kreddy-nelakurti/UniQHW/Components/KP15B-6S-SF_800_/KP15B-6S-SF_800_.step

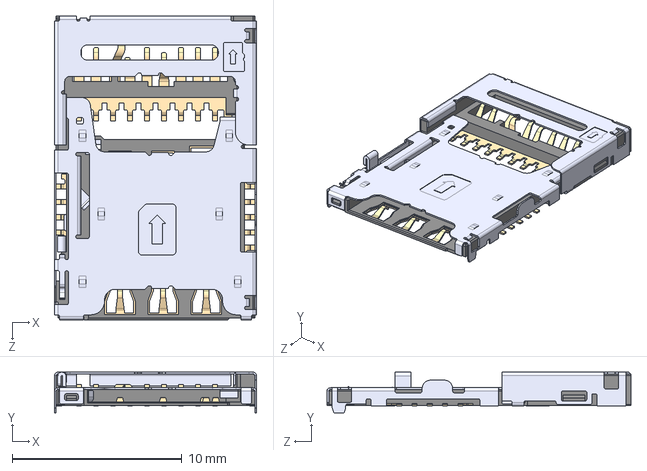
[picture p15: CAD file, 2026-02-27]
Components/KP15B-6S-SF_800_/KP15B-6S-SF_800_.step
11.9 x 2.40 x 17.9 mm
