kreddy-nelakurti/UniQHW/Components/LightOn-LEDs/LTST-C193KRKT-5A.step

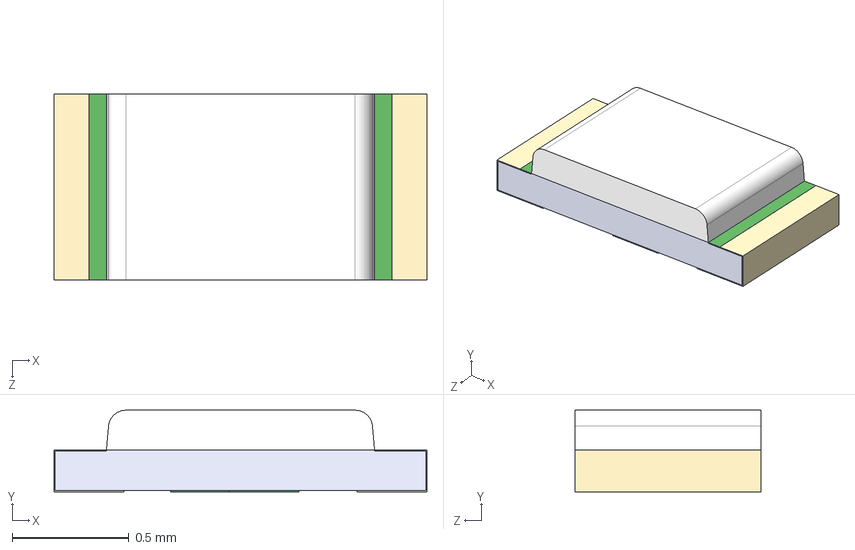
[picture p16: CAD file, 2026-02-27]
Components/LightOn-LEDs/LTST-C193KRKT-5A.step
1.60 x 0.35 x 0.8 mm
