kreddy-nelakurti/UniQHW/Components/MMBT3904LP-7/MMBT3904LP-7.step

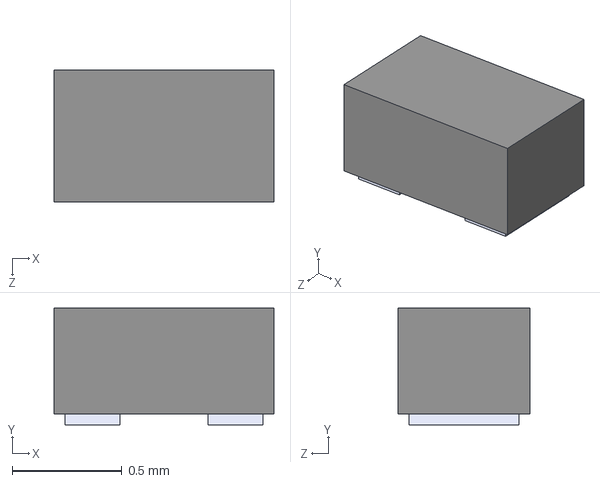
[picture p17: CAD file, 2026-02-27]
Components/MMBT3904LP-7/MMBT3904LP-7.step
1.00 x 0.53 x 0.6 mm
