kreddy-nelakurti/UniQHW/Components/MMBT3904LT1G/MMBT3904LT1G.step

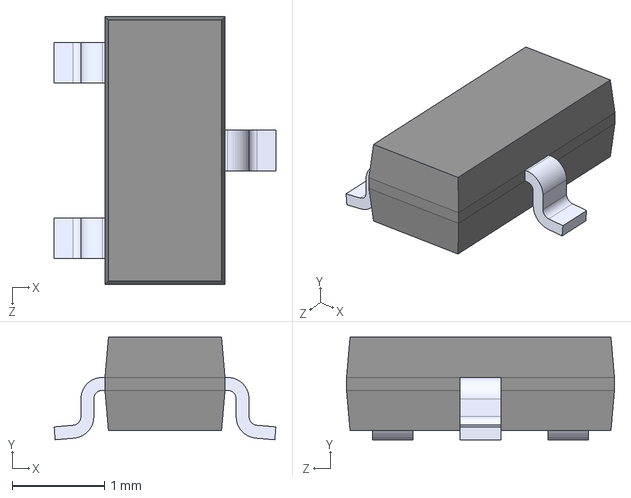
[picture p18: CAD file, 2026-02-27]
Components/MMBT3904LT1G/MMBT3904LT1G.step
2.40 x 1.11 x 2.90 mm
