kreddy-nelakurti/UniQHW/Components/MMSZ5231BT1G/SOD-123_ONS.step

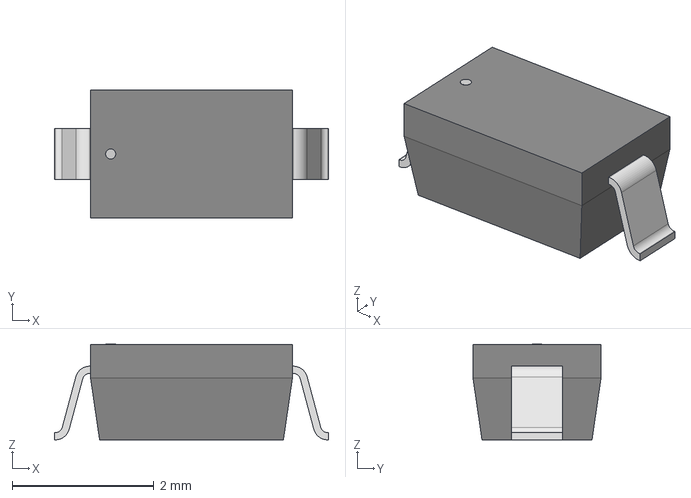
[picture p19: CAD file, 2026-02-27]
Components/MMSZ5231BT1G/SOD-123_ONS.step
3.86 x 1.80 x 1.35 mm
