kreddy-nelakurti/UniQHW/Components/MPZ2012S221AT000/MPZ2012S221AT000.step

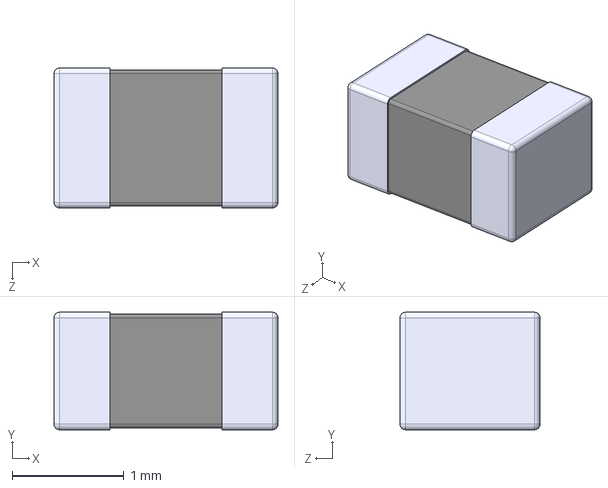
[picture p20: CAD file, 2026-02-27]
Components/MPZ2012S221AT000/MPZ2012S221AT000.step
2.00 x 1.05 x 1.25 mm
