kreddy-nelakurti/UniQHW/Components/PCA9306DQER/PCA9306DQER.step

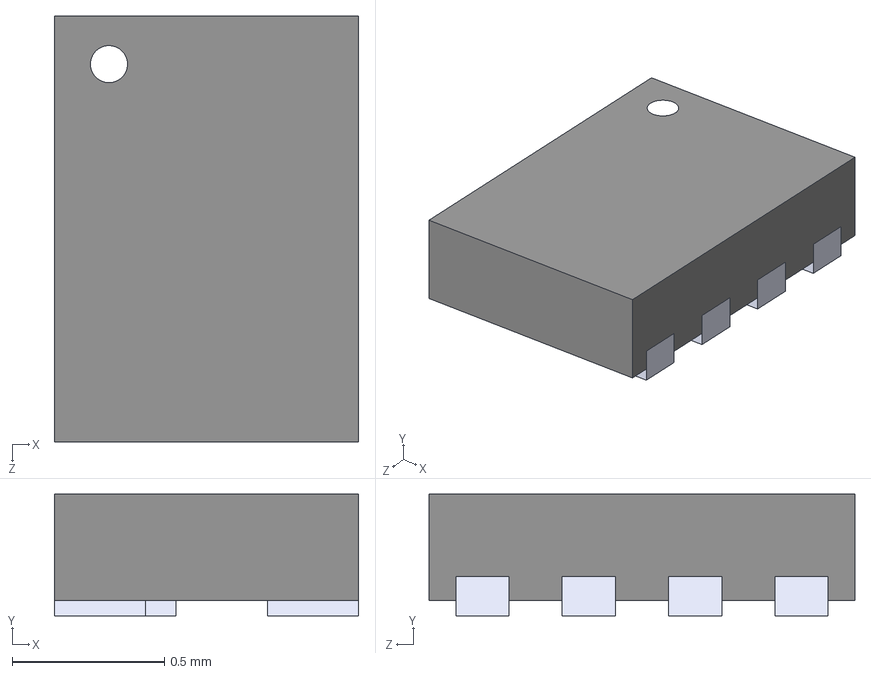
[picture p21: CAD file, 2026-02-27]
Components/PCA9306DQER/PCA9306DQER.step
1.00 x 0.4 x 1.40 mm
