kreddy-nelakurti/UniQHW/Components/S3B-PH-SM4-TB_LF__SN_/S3B-PH-SM4-TB_LF__SN_.step

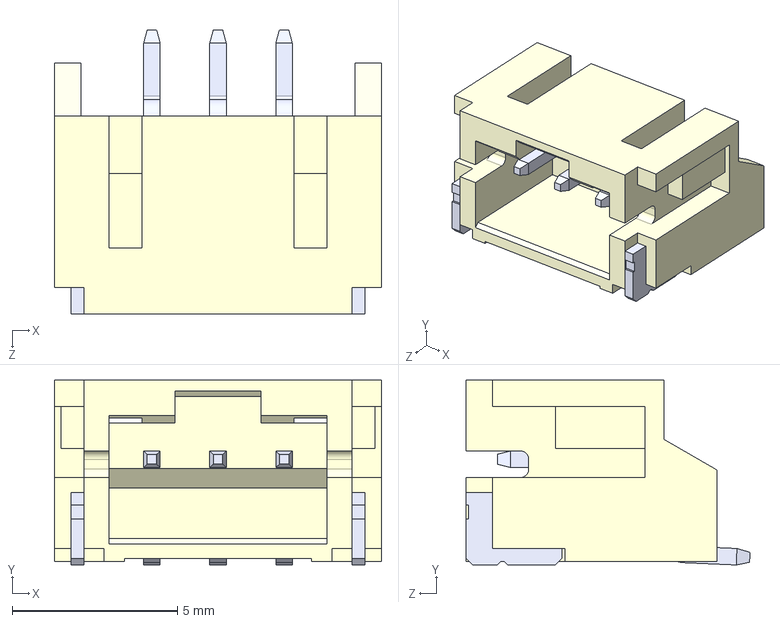
[picture p22: CAD file, 2026-02-27]
Components/S3B-PH-SM4-TB_LF__SN_/S3B-PH-SM4-TB_LF__SN_.step
9.90 x 5.60 x 8.60 mm
