kreddy-nelakurti/UniQHW/Components/SJ-3551B-MSMT-TR-67/SJ-3551B-MSMT-TR-67.step

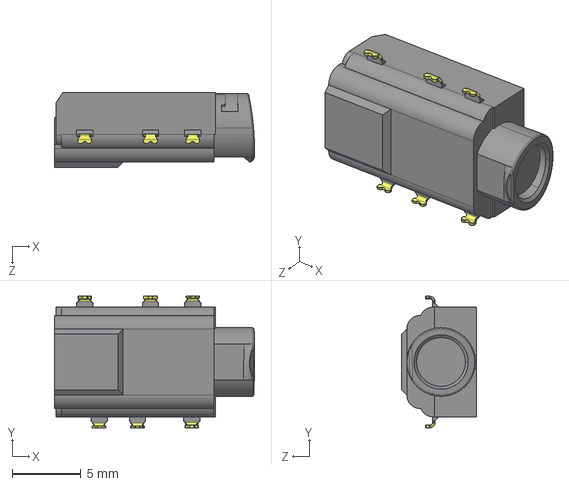
[picture p23: CAD file, 2026-02-27]
Components/SJ-3551B-MSMT-TR-67/SJ-3551B-MSMT-TR-67.step
14.6 x 9.60 x 5.45 mm
