kreddy-nelakurti/UniQHW/Components/SJ-43504-SMT-TR/SJ-43504-SMT-TR.step

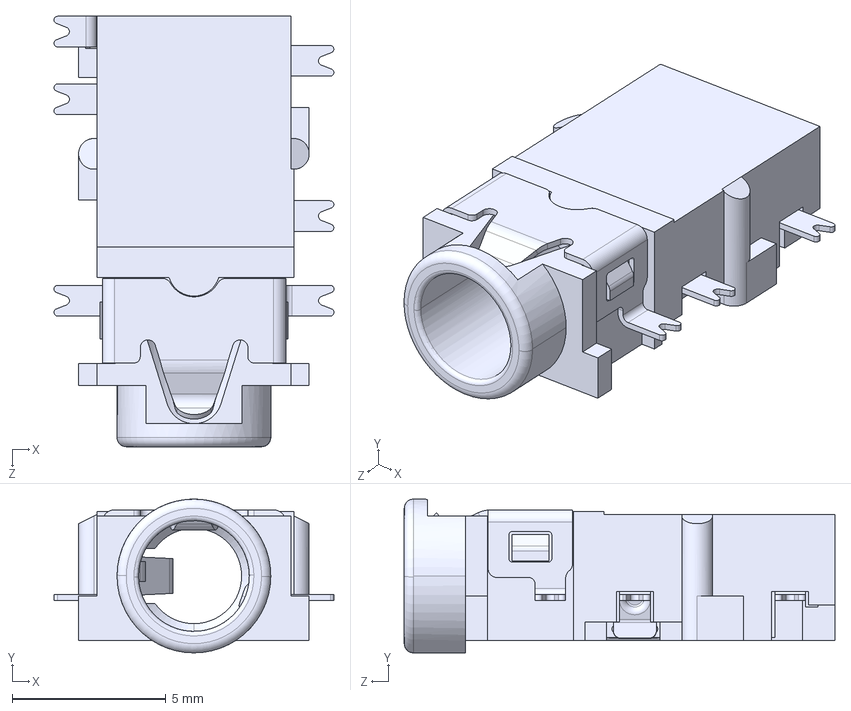
[picture p24: CAD file, 2026-02-27]
Components/SJ-43504-SMT-TR/SJ-43504-SMT-TR.step
9.10 x 5.00 x 14.0 mm
