kreddy-nelakurti/UniQHW/Components/SJ-43515RS-SMT-TR/SJ-43515RS-SMT-TR.step

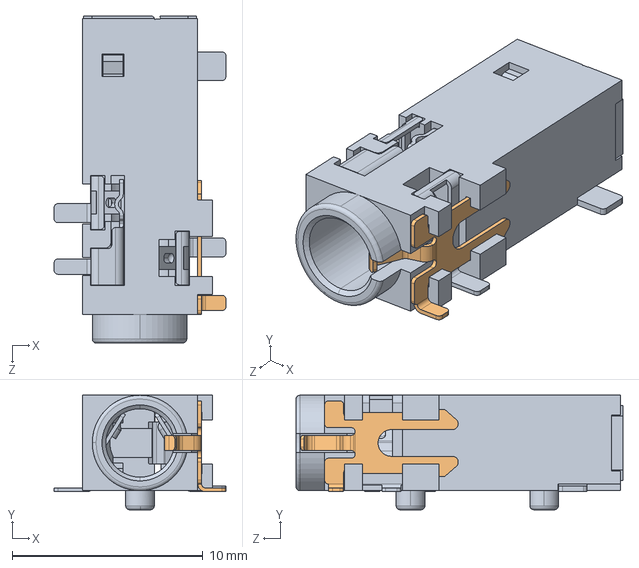
[picture p25: CAD file, 2026-02-27]
Components/SJ-43515RS-SMT-TR/SJ-43515RS-SMT-TR.step
9.00 x 6.00 x 17.1 mm
