kreddy-nelakurti/UniQHW/Components/SJ-43615TS-SMT/SJ-43615TS-SMT.step

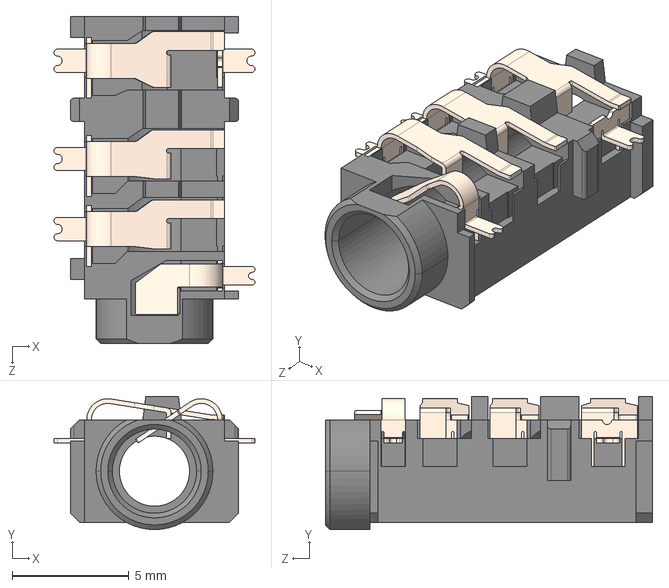
[picture p26: CAD file, 2026-02-27]
Components/SJ-43615TS-SMT/SJ-43615TS-SMT.step
8.60 x 5.70 x 14.0 mm
