kreddy-nelakurti/UniQHW/Components/SMD-TRANSISTORS-NPN-25V-500MW_SOT-23_/SMD-TRANSISTORS-NPN-25V-500MW_SOT-23_.step

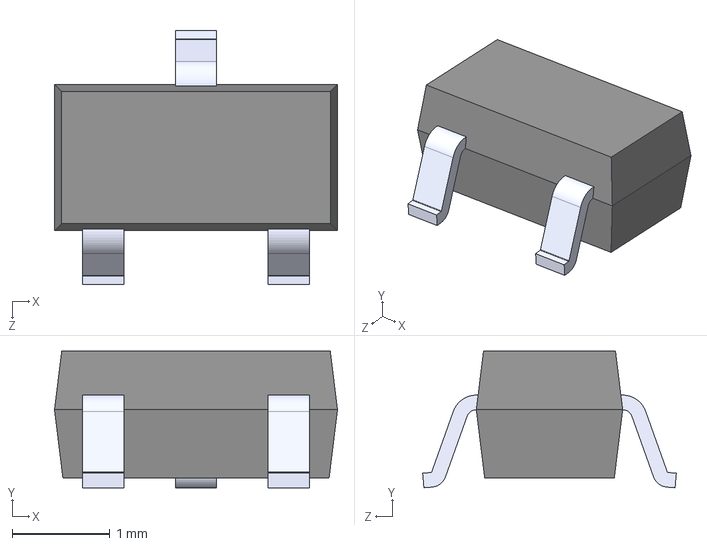
[picture p27: CAD file, 2026-02-27]
Components/SMD-TRANSISTORS-NPN-25V-500MW_SOT-23_/SMD-TRANSISTORS-NPN-25V-500MW_SOT-23_.step
2.90 x 1.40 x 2.60 mm
