kreddy-nelakurti/UniQHW/Components/SP0503BAHTG/SP0503BAHTG.step

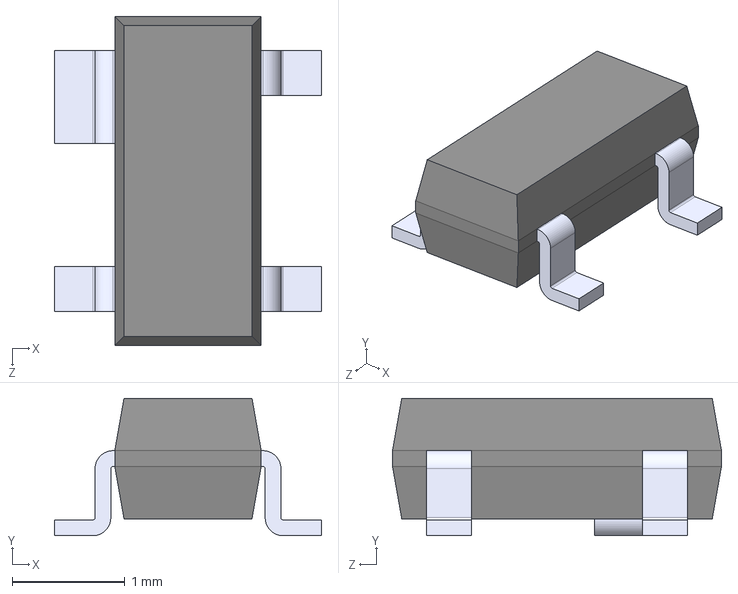
[picture p28: CAD file, 2026-02-27]
Components/SP0503BAHTG/SP0503BAHTG.step
2.37 x 1.22 x 2.92 mm
