kreddy-nelakurti/UniQHW/Components/TC2050-IDC/TC2050-IDC.step

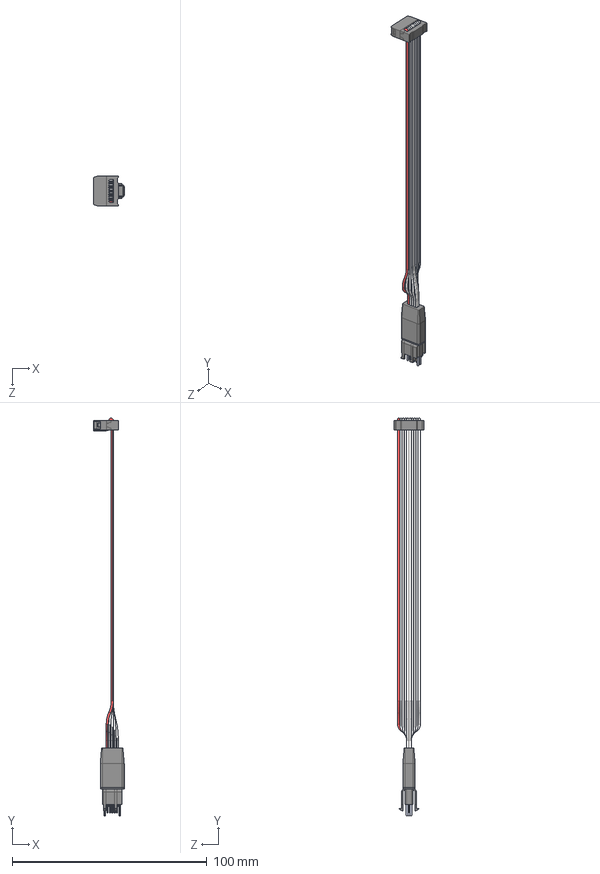
[picture p29: CAD file, 2026-02-27]
Components/TC2050-IDC/TC2050-IDC.step
15.7 x 204.4 x 15.2 mm
