kreddy-nelakurti/UniQHW/Components/TCA9509MRVHR/RVH0008A.stp

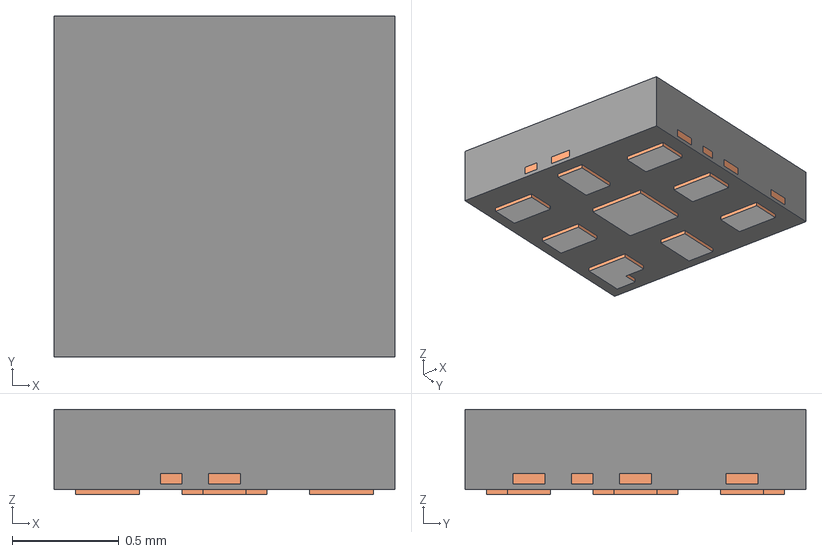
[picture p30: CAD file, 2026-02-27]
Components/TCA9509MRVHR/RVH0008A.stp
1.60 x 1.60 x 0.4 mm
BODY-QFN
FRAME-RVH0008A
PIN1-ID
