kreddy-nelakurti/UniQHW/Components/TPD3F303DQDR/TPD3F303DQDR.step

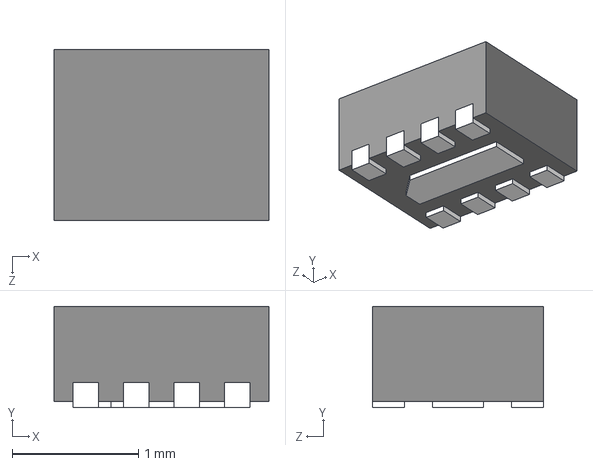
[picture p31: CAD file, 2026-02-27]
Components/TPD3F303DQDR/TPD3F303DQDR.step
1.70 x 0.8 x 1.35 mm
