kreddy-nelakurti/UniQHW/Components/TS3A5018RSVR/TS3A5018RSVR.step

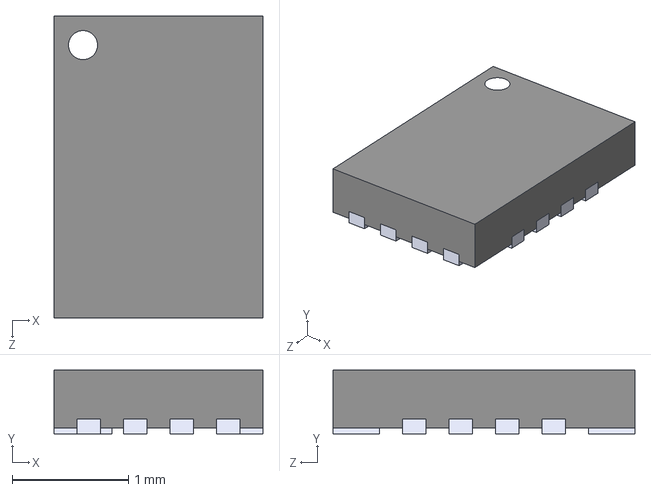
[picture p32: CAD file, 2026-02-27]
Components/TS3A5018RSVR/TS3A5018RSVR.step
1.80 x 0.55 x 2.60 mm
