kreddy-nelakurti/UniQHW/Components/TXB0108RGYR/TXB0108RGYR.step

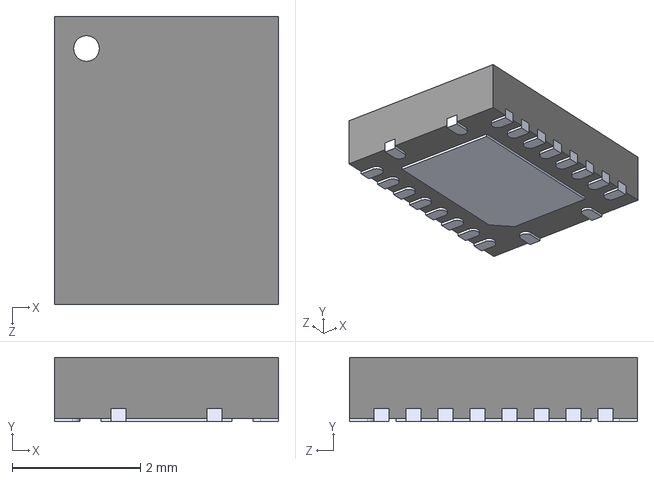
[picture p33: CAD file, 2026-02-27]
Components/TXB0108RGYR/TXB0108RGYR.step
3.50 x 1.00 x 4.50 mm
