kreddy-nelakurti/UniQHW/Components/TXB0108YZPR2/YZP20.step

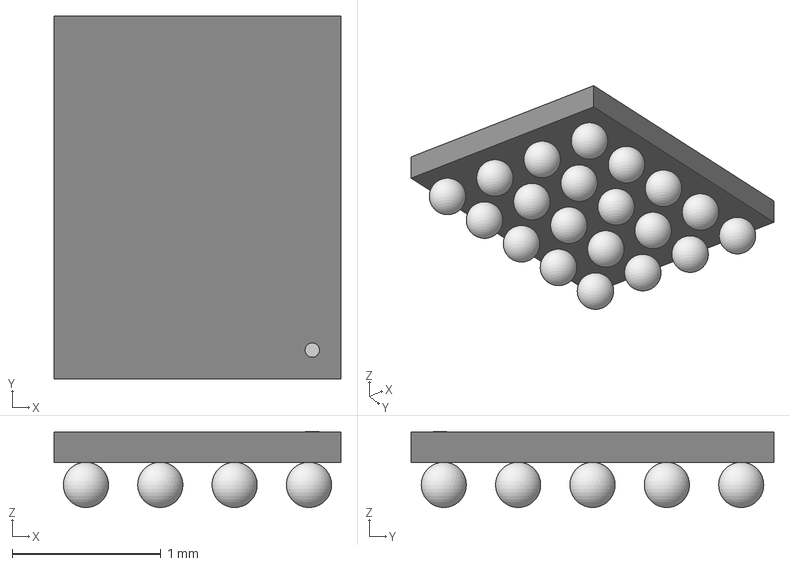
[picture p34: CAD file, 2026-02-27]
Components/TXB0108YZPR2/YZP20.step
1.93 x 2.44 x 0.511 mm
