kreddy-nelakurti/UniQHW/Components/TXU0x04DTRR/RUT0012A.stp

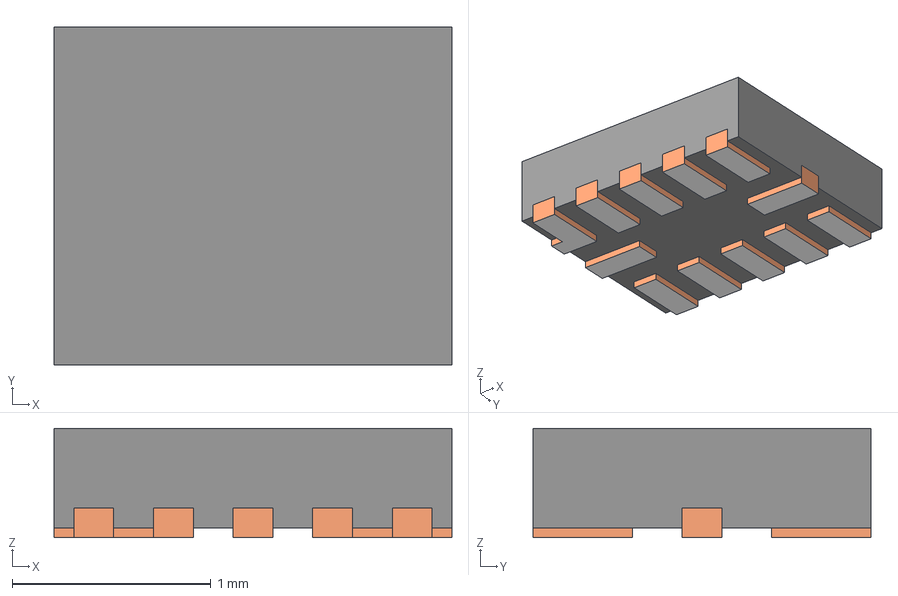
[picture p35: CAD file, 2026-02-27]
Components/TXU0x04DTRR/RUT0012A.stp
2.00 x 1.70 x 0.55 mm
BODY-SON
FRAME-RUT0012A
PIN1-ID
