kreddy-nelakurti/UniQHW/Components/USB_C_connector/USB4105-GF-A.step

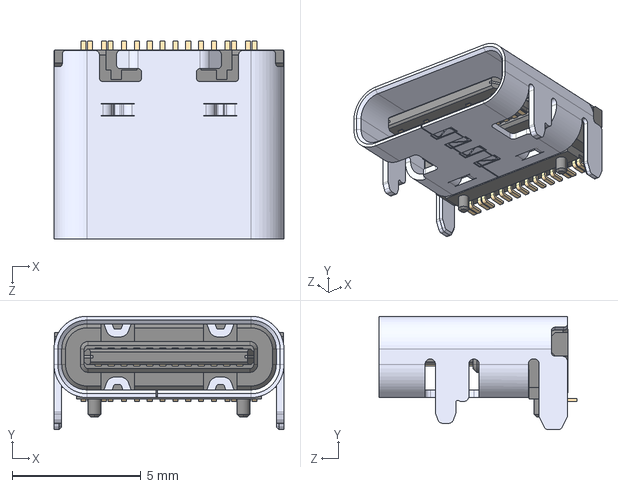
[picture p36: CAD file, 2026-02-27]
Components/USB_C_connector/USB4105-GF-A.step
8.94 x 4.41 x 7.71 mm
