kreddy-nelakurti/UniQHW/uq_phone_v0.2.0/uq_phone.step

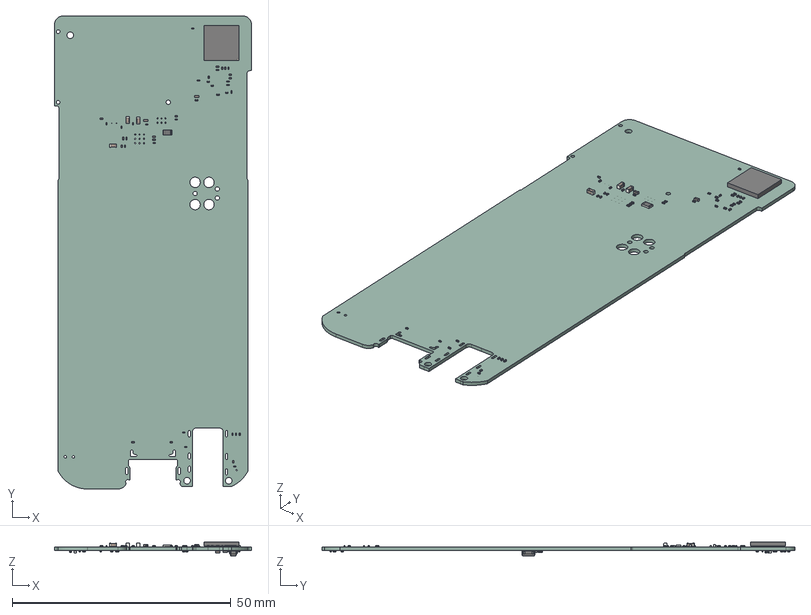
[picture p37: CAD file, 2026-09-22]
uq_phone_v0.2.0/uq_phone.step
45.0 x 108.0 x 3.23 mm
R_0201_0603Metric x 23
C_0201_0603Metric x 40
C_0603_1608Metric x 3
C_0402_1005Metric x 5
TFBGA-100_8x8mm_Layout10x10_P0.8mm
R_0805_2012Metric
R_0402_1005Metric x 3
SOT-23
uq_phone_PCB
