kreddy-nelakurti/UniQHW/uq_phone_v0.2.0/uq_phone_subboards/uq_phone_cellular/uq_phone_cellular.step

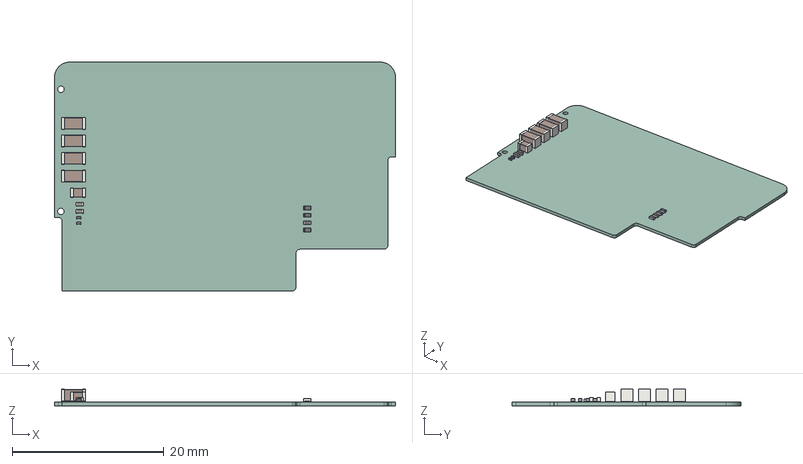
[picture p38: CAD file, 2026-09-22]
uq_phone_v0.2.0/uq_phone_subboards/uq_phone_cellular/uq_phone_cellular.step
45.0 x 30.2 x 2.20 mm
R_0402_1005Metric x 4
C_1206_3216Metric x 4
C_0805_2012Metric
C_0402_1005Metric x 2
C_0201_0603Metric x 2
uq_phone_cellular_PCB
