kreddy-nelakurti/UniQHW/uq_phone_v0.2.0/uq_phone_subboards/uq_phone_headphone/uq_phone_headphone_jack.step

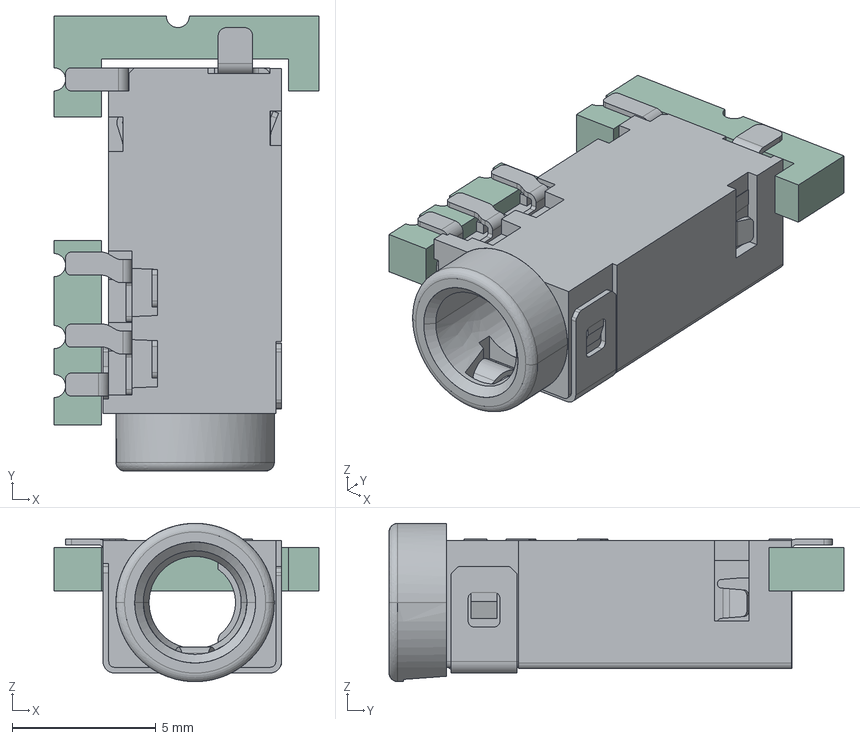
[picture p39: CAD file, 2026-09-16]
uq_phone_v0.2.0/uq_phone_subboards/uq_phone_headphone/uq_phone_headphone_jack.step
9.20 x 15.8 x 5.50 mm
STX_3542_5N_G_TR_A
uq_phone_headphone_jack_PCB_1
uq_phone_headphone_jack_PCB_2
