kreddy-nelakurti/UniQHW/Components/TXU0x04DTRR/DTR0012A.stp

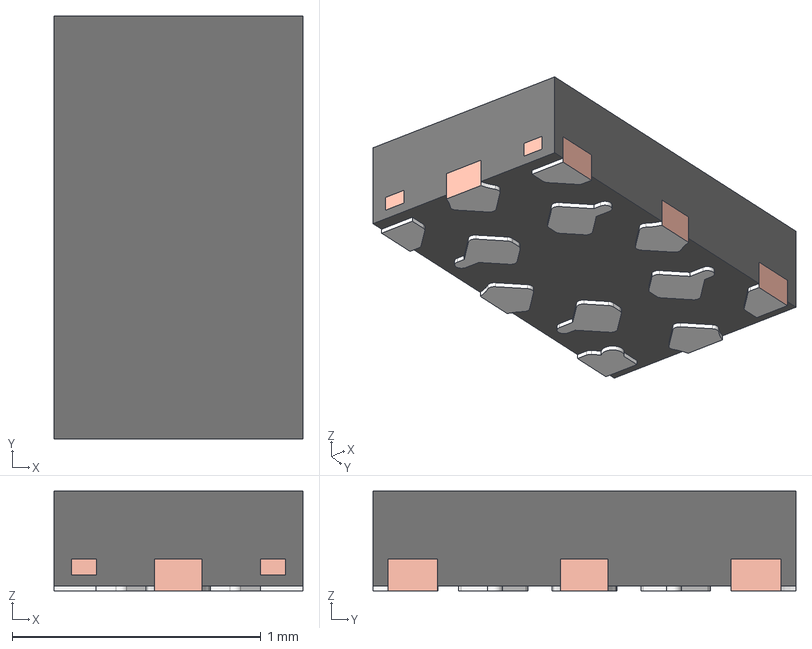
[picture p40: CAD file, 2026-02-27]
Components/TXU0x04DTRR/DTR0012A.stp
1.00 x 1.70 x 0.4 mm
FRAME
MOLD
