kreddy-nelakurti/UniQHW/Components/custom_footprints_3d/MCABS-258-RC.step

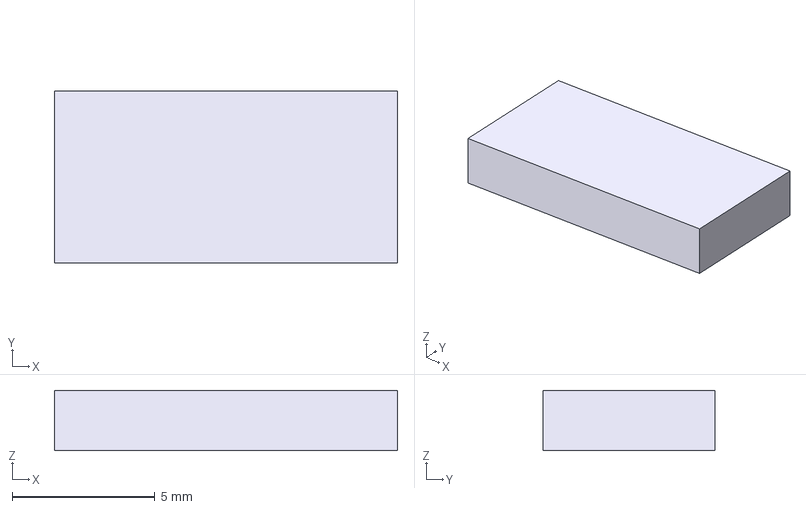
[picture p41: CAD file, 2026-02-27]
Components/custom_footprints_3d/MCABS-258-RC.step
12.0 x 6.00 x 2.10 mm
