kreddy-nelakurti/UniQHW/Components/custom_footprints_3d/pj-342D.step

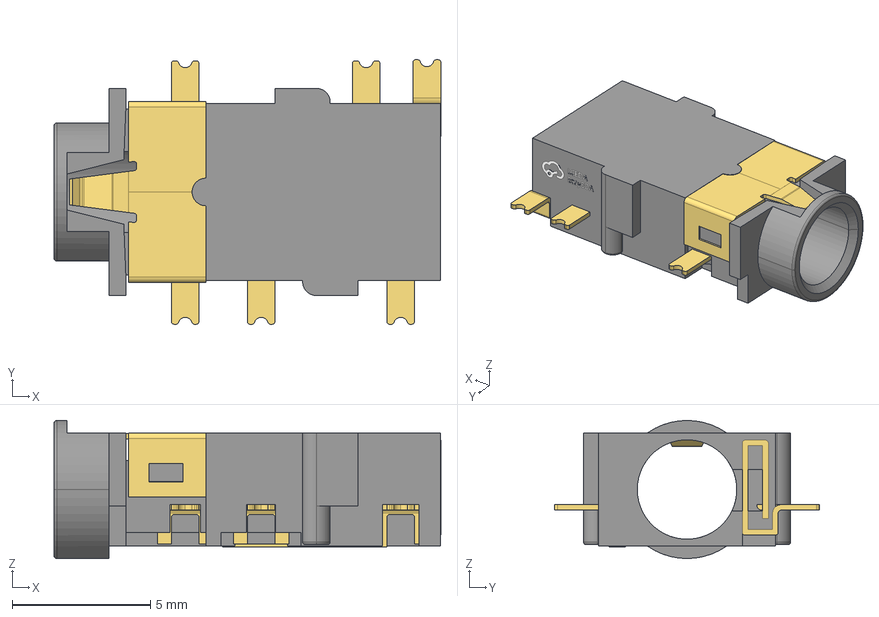
[picture p42: CAD file, 2026-02-27]
Components/custom_footprints_3d/pj-342D.step
14.0 x 9.58 x 5.00 mm
AUDIO-SMD_PJ-342D~AUDIO-SMD_PJ-342D~lkpv
AUDIO-SMD_PJ-342D~AUDIO-SMD_PJ-342D~lkpv001
AUDIO-SMD_PJ-342D~AUDIO-SMD_PJ-342D~lkpv002
AUDIO-SMD_PJ-342D~AUDIO-SMD_PJ-342D~lkpv003
AUDIO-SMD_PJ-342D~AUDIO-SMD_PJ-342D~lkpv004
AUDIO-SMD_PJ-342D~AUDIO-SMD_PJ-342D~lkpv005
AUDIO-SMD_PJ-342D~AUDIO-SMD_PJ-342D~lkpv006
AUDIO-SMD_PJ-342D~AUDIO-SMD_PJ-342D~lkpv007
AUDIO-SMD_PJ-342D~AUDIO-SMD_PJ-342D~lkpv008
