kreddy-nelakurti/UniQHW/Components/custom_footprints_3d/PJ-605.step

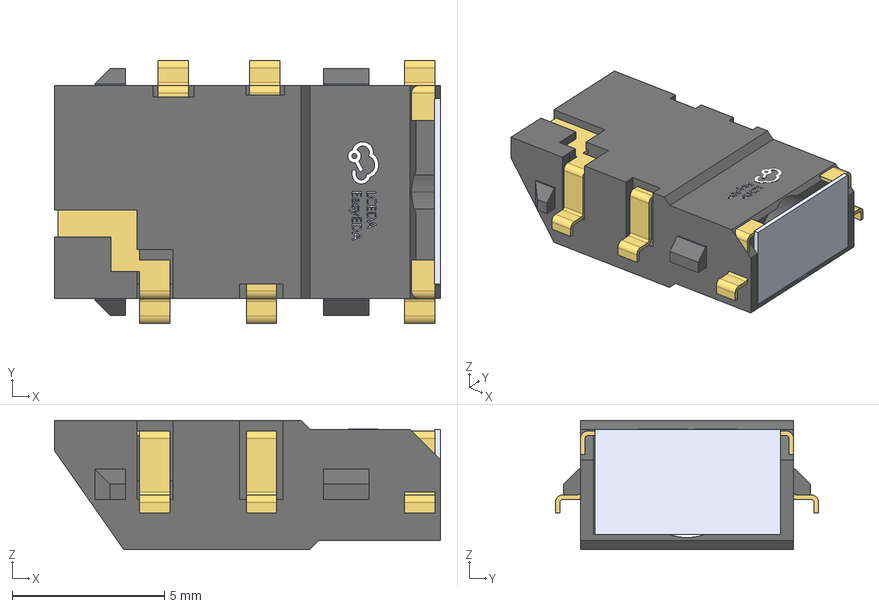
[picture p43: CAD file, 2026-02-27]
Components/custom_footprints_3d/PJ-605.step
12.7 x 8.65 x 4.25 mm
AUDIO-TH_PJ-605-6A~AUDIO-TH_PJ-605-6A~5Nou
AUDIO-TH_PJ-605-6A~AUDIO-TH_PJ-605-6A~5Nou001
AUDIO-TH_PJ-605-6A~AUDIO-TH_PJ-605-6A~5Nou002
AUDIO-TH_PJ-605-6A~AUDIO-TH_PJ-605-6A~5Nou003
AUDIO-TH_PJ-605-6A~AUDIO-TH_PJ-605-6A~5Nou004
AUDIO-TH_PJ-605-6A~AUDIO-TH_PJ-605-6A~5Nou005
AUDIO-TH_PJ-605-6A~AUDIO-TH_PJ-605-6A~5Nou006
AUDIO-TH_PJ-605-6A~AUDIO-TH_PJ-605-6A~5Nou007
