kreddy-nelakurti/UniQHW/Components/custom_footprints_3d/SKTAAAE010.STEP

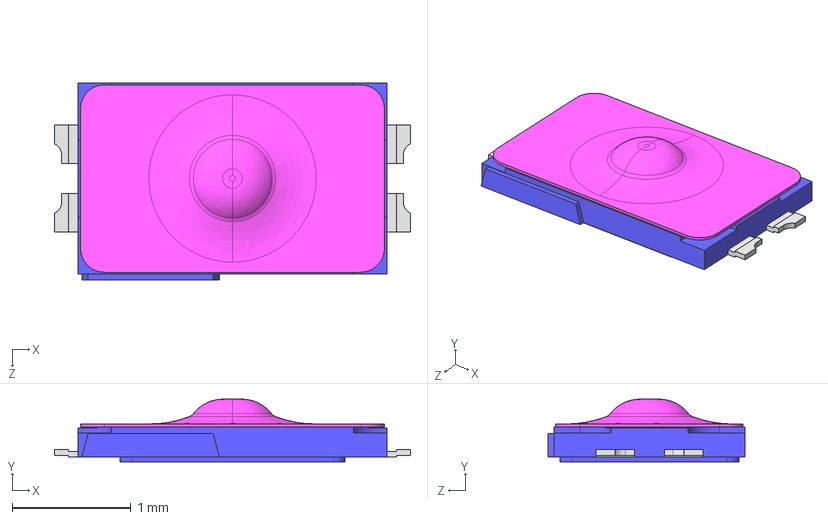
[picture p44: CAD file, 2026-02-27]
Components/custom_footprints_3d/SKTAAAE010.STEP
3.00 x 0.53 x 1.66 mm
