kreddy-nelakurti/UniQHW/Components/custom_footprints_3d/SKSCLC.STEP

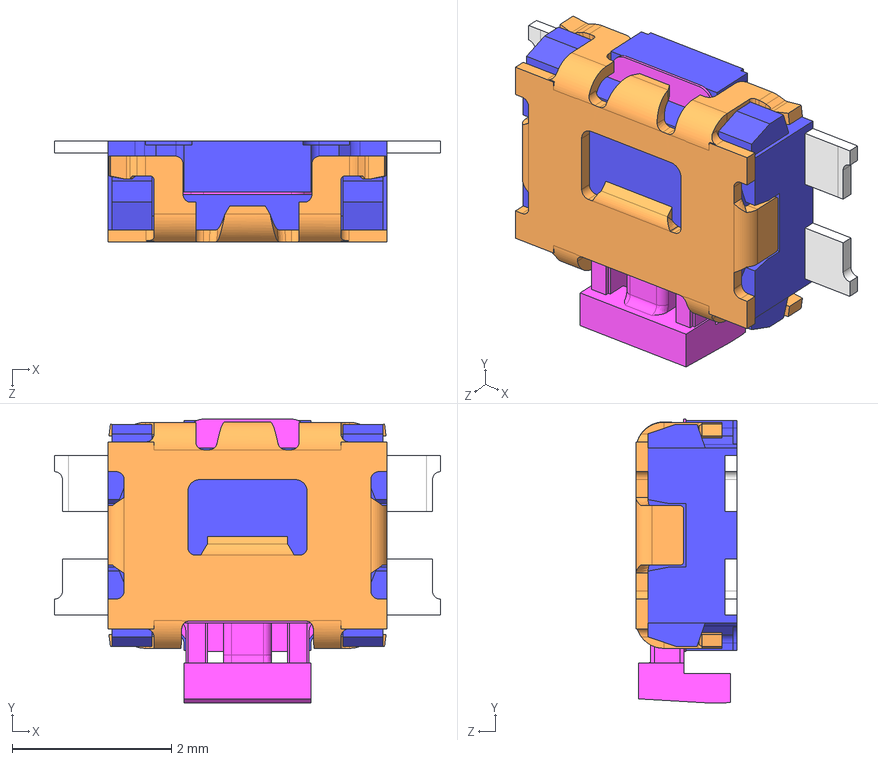
[picture p45: CAD file, 2026-02-27]
Components/custom_footprints_3d/SKSCLC.STEP
4.85 x 3.56 x 1.27 mm
